colas-sebastien/M5atom-motion-Wall-E/img/i2c_motor_top_pin.jpg

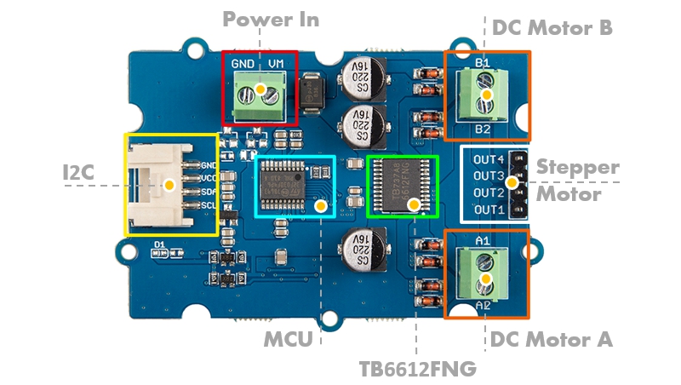
img/i2c_motor_top_pin.jpg
