colas-sebastien/M5atom-motion-Wall-E/img/tailbat.jpg

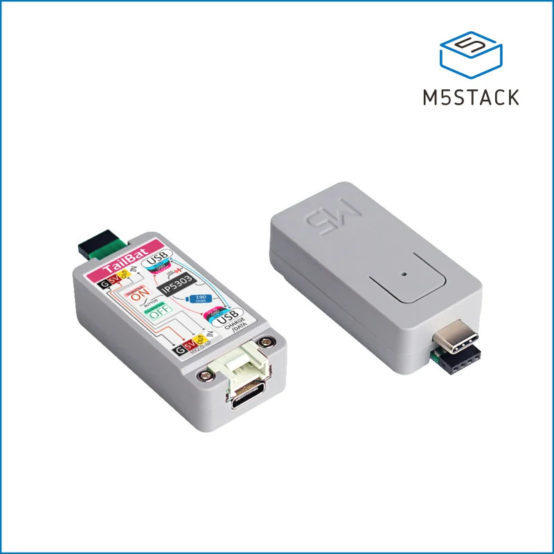
img/tailbat.jpg
